artigiadigital/Lombricolage/V30 serbatoio e piedini/stl/v30_colla_set_zampe_e_piedini.stl

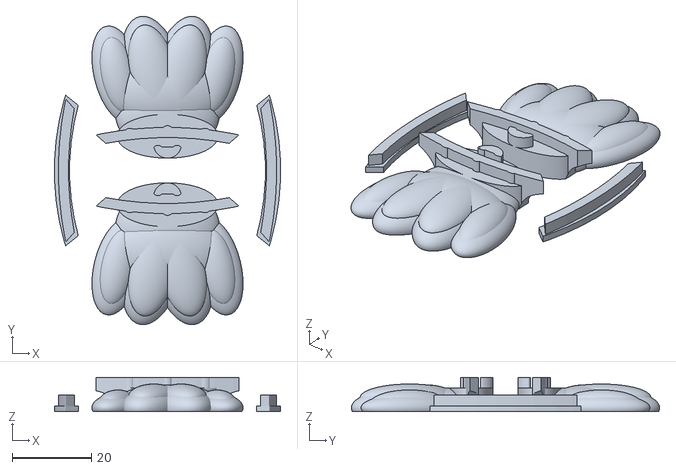
[picture p31: CAD file, 2018-06-12]
V30 serbatoio e piedini/stl/v30_colla_set_zampe_e_piedini.stl
57.0 x 77.8 x 8.70
